ecquack/Project68/PIC18/80columnvideo/80font.c

// Copyright (C) 2010 Trigonoetics Instruments, Inc.
//
// font for 80column video.
// font is 8x8 256 characters interleave so that the first
// 256 bytes are for line 0, the second 256 bytes are for line 1,
// etc.
//
// right now it's characters 32-127 plus
// the inverted video versions at 160-255.
// 
// straight ASCII. Character 127 is a degree symbol (temperature)
// we could have 0-31 as special characters.
//
// we intend to use inverse video for a cursor which could blink
//
// the vertical strokes look a little thin in NTSC. This is partly due to
// scaling on the LCD monitor


#rom int8 0x2000={
   0x00, 0x00, 0x00, 0x00, 0x00, 0x00, 0x00, 0x00, // 0x000
   0x00, 0x00, 0x00, 0x00, 0x00, 0x00, 0x00, 0x00, // 0x008
   0x00, 0x00, 0x00, 0x00, 0x00, 0x00, 0x00, 0x00, // 0x010
   0x00, 0x00, 0x00, 0x00, 0x00, 0x00, 0x00, 0x00, // 0x018
   0x00, 0x08, 0x14, 0x14, 0x1c, 0x26, 0x0c, 0x10, // 0x020
   0x10, 0x04, 0x00, 0x00, 0x00, 0x00, 0x00, 0x20, // 0x028
   0x1c, 0x08, 0x1c, 0x1c, 0x10, 0x3e, 0x18, 0x3e, // 0x030
   0x1c, 0x1c, 0x00, 0x00, 0x20, 0x00, 0x04, 0x1c, // 0x038
   0x1c, 0x08, 0x1e, 0x1c, 0x0e, 0x3e, 0x3e, 0x1c, // 0x040 64 blah: we start grabbing characters from 0x1e,0x1c,0x0e,0x3e....
   0x22, 0x1c, 0x38, 0x22, 0x04, 0x22, 0x22, 0x1c, // 0x048
   0x1e, 0x1c, 0x1e, 0x1c, 0x3e, 0x22, 0x22, 0x41, // 0x050
   0x22, 0x22, 0x3e, 0x1c, 0x02, 0x1c, 0x00, 0x00, // 0x058
   0x08, 0x00, 0x02, 0x00, 0x20, 0x00, 0x10, 0x00, // 0x060
   0x02, 0x08, 0x10, 0x04, 0x0c, 0x00, 0x00, 0x00, // 0x068
   0x00, 0x00, 0x00, 0x00, 0x00, 0x00, 0x00, 0x00, // 0x070
   0x00, 0x00, 0x00, 0x10, 0x08, 0x04, 0x00, 0x00, // 0x078
   0xff, 0xff, 0xff, 0xff, 0xff, 0xff, 0xff, 0xff, // 0x080 128
   0xff, 0xff, 0xff, 0xff, 0xff, 0xff, 0xff, 0xff, // 0x088
   0xff, 0xff, 0xff, 0xff, 0xff, 0xff, 0xff, 0xff, // 0x090
   0xff, 0xff, 0xff, 0xff, 0xff, 0xff, 0xff, 0xff, // 0x098
   0xff, 0xf7, 0xeb, 0xeb, 0xe3, 0xd9, 0xf3, 0xef, // 0x0A0 160
   0xef, 0xfb, 0xff, 0xff, 0xff, 0xff, 0xff, 0xdf, // 0x0A8
   0xe3, 0xf7, 0xe3, 0xe3, 0xef, 0xc1, 0xe7, 0xc1, // 0x0B0
   0xe3, 0xe3, 0xff, 0xff, 0xdf, 0xff, 0xfb, 0xe3, // 0x0B8
   0xe3, 0xf7, 0xe1, 0xe3, 0xf1, 0xc1, 0xc1, 0xe3, // 0x0C0
   0xdd, 0xe3, 0xc7, 0xdd, 0xfb, 0xdd, 0xdd, 0xe3, // 0x0C8
   0xe1, 0xe3, 0xe1, 0xe3, 0xc1, 0xdd, 0xdd, 0xbe, // 0x0D0
   0xdd, 0xdd, 0xc1, 0xe3, 0xfd, 0xe3, 0xff, 0xff, // 0x0D8
   0xf7, 0xff, 0xfd, 0xff, 0xdf, 0xff, 0xef, 0xff, // 0x0E0
   0xfd, 0xf7, 0xef, 0xfb, 0xf3, 0xff, 0xff, 0xff, // 0x0E8
   0xff, 0xff, 0xff, 0xff, 0xff, 0xff, 0xff, 0xff, // 0x0F0
   0xff, 0xff, 0xff, 0xef, 0xf7, 0xfb, 0xff, 0xff, // 0x0F8
   0x00, 0x00, 0x00, 0x00, 0x00, 0x00, 0x00, 0x00, // 0x100 256
   0x00, 0x00, 0x00, 0x00, 0x00, 0x00, 0x00, 0x00, 
   0x00, 0x00, 0x00, 0x00, 0x00, 0x00, 0x00, 0x00, 
   0x00, 0x00, 0x00, 0x00, 0x00, 0x00, 0x00, 0x00, 
   0x00, 0x08, 0x14, 0x14, 0x2a, 0x26, 0x12, 0x10, 
   0x08, 0x08, 0x14, 0x08, 0x00, 0x00, 0x00, 0x20, 
   0x22, 0x0c, 0x22, 0x22, 0x18, 0x02, 0x04, 0x20, 
   0x22, 0x22, 0x00, 0x00, 0x10, 0x00, 0x08, 0x22, 
   0x22, 0x14, 0x22, 0x22, 0x12, 0x02, 0x02, 0x22, 
   0x22, 0x08, 0x10, 0x12, 0x04, 0x36, 0x26, 0x22, 
   0x22, 0x22, 0x22, 0x22, 0x08, 0x22, 0x22, 0x41, 
   0x22, 0x22, 0x20, 0x04, 0x02, 0x10, 0x08, 0x00, 
   0x08, 0x00, 0x02, 0x00, 0x20, 0x00, 0x28, 0x00, 
   0x02, 0x00, 0x00, 0x04, 0x08, 0x00, 0x00, 0x00, 
   0x00, 0x00, 0x00, 0x00, 0x08, 0x00, 0x00, 0x00, 
   0x00, 0x00, 0x00, 0x08, 0x08, 0x08, 0x4c, 0x00, 
   0xff, 0xff, 0xff, 0xff, 0xff, 0xff, 0xff, 0xff, 
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
}
