ecquack/Project68/PIC18/80columnvideo/flipscancodes.c

const char flipcodes[]={
0  ,0  ,0x00,   //00 0x00
0  ,0  ,0x00,   //01 0x40
0  ,0  ,0x00,   //02 0x20
0  ,0  ,0x00,   //03 0x60
0  ,0  ,0x00,   //04 0x10
0  ,0  ,0x00,   //05 0x50
0  ,0  ,0x00,   //06 0x30
0  ,0  ,0x00,   //07 0x70 key release & keypad zero (0x07)
0  ,0  ,0x00,   //08 0x08
0  ,0  ,0x00,   //09 0x48
0  ,0  ,0x00,   //0a 0x28
0  ,0  ,0x00,   //0b 0x68
0  ,0  ,0x00,   //0c 0x18
0  ,0  ,0x00,   //0d 0x58 CAPS LOCK
0  ,0  ,0x00,   //0e 0x38
0  ,0  ,0x8B,   //0f 0x78 F11
0  ,0  ,0x83,   //10 0x04 F3
'o','O',0x0f,   //11 0x44
'e','E',0x05,   //12 0x24
0  ,0  ,0x00,   //13 0x64
0  ,0  ,0x00,   //14 0x14
'[','{',0x00,   //15 0x54
'g','G',0x07,   //16 0x34
'6','Ç',0x00,   //17 0x74
0  ,0  ,0x84,   //18 0x0C F4
';',':',0x00,   //19 0x4C
't','T',0x14,   //1a 0x2C
'7',',',0x00,   //1b 0x6C
'a','A',0x01,   //1c 0x1C
0  ,0  ,0x00,   //1d 0x5C
'u','U',0x15,   //1e 0x3C
'*',0  ,0x00,   //1f 0x7C
0  ,0  ,0x00,   //20 0x02
'k','K',0x0b,   //21 0x42
'x','X',0x18,   //22 0x22
0  ,0  ,0x00,   //23 0x62
0  ,0  ,0x00,   //24 0x12 LEFT SHIFT
'\'','\"',0x00, //25 0x52 QUOTES
'b','B',0x02,   //26 0x32 extended volume up
'2',',',0x00,   //27 0x72
0  ,0  ,0x88,   //28 0x0A
'/',0  ,0x80,   //29 0x4A
'v','V',0x16,   //2a 0x2A
0  ,0  ,0x00,   //2b 0x6A
'z','Z',0x1a,   //2c 0x1A
0  ,0  ,0x80,   //2d 0x5A ENTER
'm','M',0x0d,   //2e 0x3A
'3',',',0x00,   //2f 0x7A
0  ,0  ,0x80,   //30 0x06 F2
'9','(',0x00,   //31 0x46
'3','#',0x00,   //32 0x26
0  ,0  ,0x08,   //33 0x66
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
#define LCTRL     20 //       0x14
#define RCTRL     20 // 0xE0  0x14
#define LALT         //       0x11
#define RALT         // 0xE0  0x11
#define CAPSLOCK  13 //       0x58
#define LWIN         // 0xE0  0x1F
#define RWIN         //       0x27
#define MENU         // 0xE0  0x2F
