ecquack/Project68/PIC18/80columnvideo/interrupt code.c

00000:  GOTO   MAIN
*
00008:  GOTO   00BE

0000C:  NOP
0000E:  NOP   
00010:  NOP   
00012:  NOP   
00014:  NOP   
00016:  NOP 

00018:  MOVWF  04          // start of HSYNC interrupt
0001A:  MOVFF  STATUS,05
0001E:  MOVFF  BSR,06
00022:  MOVLB  0
00024:  MOVFF  FSR0L,0C
00028:  MOVFF  FSR0H,07
0002C:  MOVFF  FSR1L,08
00030:  MOVFF  FSR1H,09
00034:  MOVFF  FSR2L,0A
00038:  MOVFF  FSR2H,0B
0003C:  MOVFF  PRODL,12
00040:  MOVFF  PRODH,13
00044:  MOVFF  PCLATH,14
00048:  MOVFF  TABLAT,15
0004C:  MOVFF  TBLPTRL,16
00050:  MOVFF  TBLPTRH,17
00054:  MOVFF  00,0E
00058:  MOVFF  01,0F
0005C:  MOVFF  02,10
00060:  MOVFF  03,11
00064:  BTFSS  PIE1.TMR2IE
00066:  GOTO   0070
0006A:  BTFSC  PIR1.TMR2IF
0006C:  GOTO   0468     // call user interrupt code

00070:  MOVFF  0E,00    // restore after interrupt
00074:  MOVFF  0F,01
00078:  MOVFF  10,02
0007C:  MOVFF  11,03
00080:  MOVFF  0C,FSR0L
00084:  MOVFF  07,FSR0H
00088:  BSF    07.7
0008A:  MOVFF  08,FSR1L
0008E:  MOVFF  09,FSR1H
00092:  MOVFF  0A,FSR2L
00096:  MOVFF  0B,FSR2H
0009A:  MOVFF  12,PRODL
0009E:  MOVFF  13,PRODH
000A2:  MOVFF  14,PCLATH
000A6:  MOVFF  15,TABLAT
000AA:  MOVFF  16,TBLPTRL
000AE:  MOVFF  17,TBLPTRH
000B2:  MOVF   04,W
000B4:  MOVFF  06,BSR
000B8:  MOVFF  05,STATUS
000BC:  RETFIE 0


000BE:  MOVWF  19          // start of PS/2 interrupt
000C0:  MOVFF  STATUS,1A
000C4:  MOVFF  BSR,1B
000C8:  MOVLB  0
000CA:  MOVFF  FSR0L,21
000CE:  MOVFF  FSR0H,1C
000D2:  MOVFF  FSR1L,1D
000D6:  MOVFF  FSR1H,1E
000DA:  MOVFF  FSR2L,1F
000DE:  MOVFF  FSR2H,20
000E2:  MOVFF  PRODL,27
000E6:  MOVFF  PRODH,28
000EA:  MOVFF  PCLATH,29
000EE:  MOVFF  TABLAT,2A
000F2:  MOVFF  TBLPTRL,2B
000F6:  MOVFF  TBLPTRH,2C
000FA:  MOVFF  00,23
000FE:  MOVFF  01,24
00102:  MOVFF  02,25
00106:  MOVFF  03,26
0010A:  BTFSS  INTCON3.INT2IE
0010C:  GOTO   0116
00110:  BTFSC  INTCON3.INT2IF
00112:  GOTO   034C     // call user interrupt code

*00116:  MOVFF  23,00    // restore after interrupt
*0011A:  MOVFF  24,01
*0011E:  MOVFF  25,02
*00122:  MOVFF  26,03
00126:  MOVFF  21,FSR0L
0012A:  MOVFF  1C,FSR0H
*0012E:  BSF    1C.7
*00130:  MOVFF  1D,FSR1L
*00134:  MOVFF  1E,FSR1H
*00138:  MOVFF  1F,FSR2L
*0013C:  MOVFF  20,FSR2H
*00140:  MOVFF  27,PRODL
*00144:  MOVFF  28,PRODH
00148:  MOVFF  29,PCLATH
0014C:  MOVFF  2A,TABLAT
00150:  MOVFF  2B,TBLPTRL
00154:  MOVFF  2C,TBLPTRH
00158:  MOVF   19,W
0015A:  MOVFF  1B,BSR
0015E:  MOVFF  1A,STATUS
00162:  RETFIE 0
//
// we can save 21 cycles on exit
// 
//

000     @SCRATCH
001     @SCRATCH
001     _RETURN_
002     @SCRATCH
003     @SCRATCH
004     @INTERRUPT_AREA
005     @INTERRUPT_AREA
006     @INTERRUPT_AREA
007     @INTERRUPT_AREA
008     @INTERRUPT_AREA
009     @INTERRUPT_AREA
00A     @INTERRUPT_AREA
00B     @INTERRUPT_AREA
00C     @INTERRUPT_AREA
00D     @INTERRUPT_AREA
00E     @INTERRUPT_AREA
00F     @INTERRUPT_AREA
010     @INTERRUPT_AREA
011     @INTERRUPT_AREA
012     @INTERRUPT_AREA
013     @INTERRUPT_AREA
014     @INTERRUPT_AREA
015     @INTERRUPT_AREA
016     @INTERRUPT_AREA
017     @INTERRUPT_AREA
018     @INTERRUPT_AREA
019     @INTERRUPT_AREA
01A     @INTERRUPT_AREA
01B     @INTERRUPT_AREA
01C     @INTERRUPT_AREA
01D     @INTERRUPT_AREA
01E     @INTERRUPT_AREA
01F     @INTERRUPT_AREA
020     @INTERRUPT_AREA
021     @INTERRUPT_AREA
022     @INTERRUPT_AREA
023     @INTERRUPT_AREA
024     @INTERRUPT_AREA
025     @INTERRUPT_AREA
026     @INTERRUPT_AREA
027     @INTERRUPT_AREA
028     @INTERRUPT_AREA
029     @INTERRUPT_AREA
02A     @INTERRUPT_AREA
02B     @INTERRUPT_AREA
02C     @INTERRUPT_AREA
02D     @INTERRUPT_AREA
02E-02F strtok.save
030-033 _Randseed
