ecquack/Project68/PIC18/80columnvideo/rawscancodes.c

const char scancodes[]={
' ',' ',0x00,   // 0x00
'F','9',0x80,   // 0x01
' ',' ',0x00,   // 0x02
'F','5',0x80,   // 0x03
'F','3',0x80,   // 0x04
'F','1',0x80,   // 0x05
'F','2',0x80,   // 0x06
'F','C',0x80,   // 0x07
' ',' ',0x00,   // 0x08
'F','A',0x80,   // 0x09
'F','8',0x80,   // 0x0A
'F','6',0x80,   // 0x0B
'F','4',0x80,   // 0x0C
' ',' ',0x09,   // 0x0D
'`','~',0x00,   // 0x0E
' ',' ',0x00,   // 0x0F
' ',' ',0x00,   // 0x10
' ',' ',0x00,   // 0x11
' ',' ',0x00,   // 0x12
' ',' ',0x00,   // 0x13
' ',' ',0x00,   // 0x14
'q','Q',0x11,   // 0x15
'1','!',0x00,   // 0x16
' ',' ',0x00,   // 0x17
' ',' ',0x00,   // 0x18
' ',' ',0x00,   // 0x19
'z','Z',0x1a,   // 0x1A
's','S',0x13,   // 0x1B
'a','A',0x01,   // 0x1C
'w','W',0x17,   // 0x1D
'2','@',0x00,   // 0x1E
' ',' ',0x00,   // 0x1F
' ',' ',0x00,   // 0x20
'c','C',0x03,   // 0x21
'x','X',0x18,   // 0x22
'd','D',0x04,   // 0x23
'e','E',0x05,   // 0x24
'4','$',0x00,   // 0x25
'3','#',0x00,   // 0x26
' ',' ',0x00,   // 0x27
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
' ',' ',0x80,   // 0x5A ENTER
']','}',0x00,   // 0x5B
' ',' ',0x00,   // 0x5C
'\\','|',0x00,  // 0x5D
' ',' ',0x00,   // 0x5E
' ',' ',0x00,   // 0x5F
' ',' ',0x00,   // 0x60
' ',' ',0x00,   // 0x61
' ',' ',0x00,   // 0x62
' ',' ',0x00,   // 0x63
' ',' ',0x00,   // 0x64
' ',' ',0x00,   // 0x65
' ',' ',0x08,   // 0x66
' ',' ',0x00,   // 0x67
' ',' ',0x00,   // 0x68
'1',' ',0x00,   // 0x69
' ',' ',0x00,   // 0x6A
'4','F',0x00,   // 0x6B
'7',' ',0x00,   // 0x6C
' ',' ',0x00,   // 0x6D
' ',' ',0x00,   // 0x6E
' ',' ',0x00,   // 0x6F
'0',' ',0x00,   // 0x70
'.',' ',0x00,   // 0x71
'2',' ',0x00,   // 0x72
'5','7',0x00,   // 0x73
'6','Ç',0x00,   // 0x74
'8',' ',0x00,   // 0x75
' ',' ',0x1b,   // 0x76
' ',' ',0x00,   // 0x77
'F','B',0x80,   // 0x78
'+',' ',0x00,   // 0x79
'3',' ',0x00,   // 0x7A
'-',' ',0x00,   // 0x7B
'*',' ',0x00,   // 0x7C
'9',' ',0x00,   // 0x7D
' ',' ',0x00,   // 0x7E
' ',' ',0x00    // 0x7F
}


char FlipBits(char inbits)
{
   int obits=0;
   
   if(inbits&0x01) obits|=0x80;
   if(inbits&0x02) obits|=0x40;
   if(inbits&0x04) obits|=0x20;
   if(inbits&0x08) obits|=0x10;
   if(inbits&0x10) obits|=0x08;
   if(inbits&0x20) obits|=0x04;
   if(inbits&0x40) obits|=0x02;
   if(inbits&0x80) obits|=0x01;

   return obits>>1;

}
