ecquack/Project68/PIC18/80columnvideo/sprintf.c

0040C:  CLRF   @01
0040E:  CLRF   @02
00410:  CLRF   @00
00412:  CLRF   @03
00414:  MOVF   @DIV1616.P1+1,W
00416:  BNZ   041C
00418:  MOVF   @DIV1616.P1,W
0041A:  BZ    044C
0041C:  MOVLW  10
0041E:  MOVWF  @@2D
00420:  BCF    STATUS.C
00422:  RLCF   ??65535,F
00424:  RLCF   ??65535+1,F
00426:  RLCF   @00,F
00428:  RLCF   @03,F
0042A:  MOVF   @DIV1616.P1+1,W
0042C:  SUBWF  @03,W
0042E:  BNZ   0434
00430:  MOVF   @DIV1616.P1,W
00432:  SUBWF  @00,W
00434:  BNC   0444
00436:  MOVF   @DIV1616.P1,W
00438:  SUBWF  @00,F
0043A:  BTFSS  STATUS.C
0043C:  DECF   @03,F
0043E:  MOVF   @DIV1616.P1+1,W
00440:  SUBWF  @03,F
00442:  BSF    STATUS.C
00444:  RLCF   @01,F
00446:  RLCF   @02,F
00448:  DECFSZ @@2D,F
0044A:  BRA    0420
0044C:  RETLW  00
0044E:  MOVFF  @sprintf_string+1,FSR0H
00452:  MOVFF  @sprintf_string,FSR0L
00456:  MOVFF  ??65535,INDF0
0045A:  INCF   FSR0L,F
0045C:  BTFSC  STATUS.Z
0045E:  INCF   FSR0H,F
00460:  CLRF   INDF0
00462:  INCF   1A,F
00464:  BTFSC  STATUS.Z
00466:  INCF   @sprintf_string+1,F
00468:  RETLW  00
0046A:  MOVFF  FSR0H,@@2F
0046E:  MOVFF  FSR0L,@@2E
00472:  BTFSS  ??65535+1.7
00474:  BRA    0486
00476:  BSF    @@2E.7
00478:  BTFSS  @@2E.4
0047A:  INCF   @@2E,F
0047C:  COMF   ??65535,F
0047E:  COMF   ??65535+1,F
00480:  INCF   ??65535,F
00482:  BTFSC  STATUS.Z
00484:  INCF   ??65535+1,F
00486:  SWAPF  ??65535+1,W
00488:  IORLW  F0
0048A:  MOVWF  @@2A
0048C:  ADDWF  @@2A,F
0048E:  ADDLW  E2
00490:  MOVWF  @@2B
00492:  ADDLW  32
00494:  MOVWF  @@2D
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
00752:  MOVLW  2E
00754:  MOVWF  ??65535
00756:  RCALL  044E
00758:  MOVLW  0C
0075A:  MOVWF  FSR0L
0075C:  MOVFF  ticks+1,??65535+1
00760:  MOVFF  ticks,??65535
00764:  RCALL  046A
....................    } 
00766:  BRA    0670
.................... } 
00768:  GOTO   07B4 (RETURN)
